mrampado/SnowballProject/InitialPrototype(Gen1)/BoardPhotos/IMG_3307.JPEG

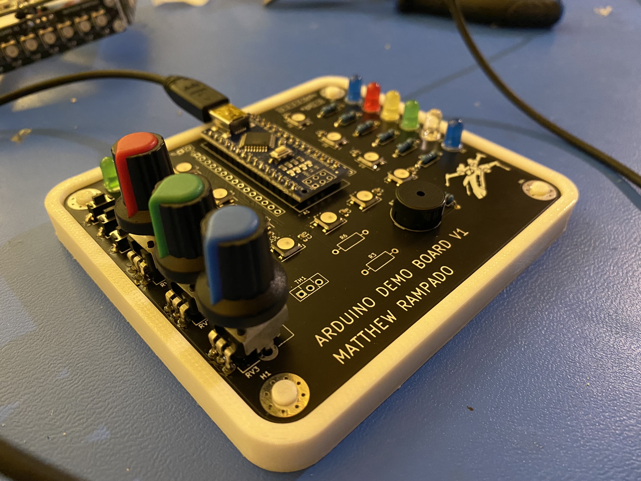
InitialPrototype(Gen1)/BoardPhotos/IMG_3307.JPEG
