mrampado/SnowballProject/InitialPrototype(Gen1)/BoardPhotos/IMG_3309.JPEG

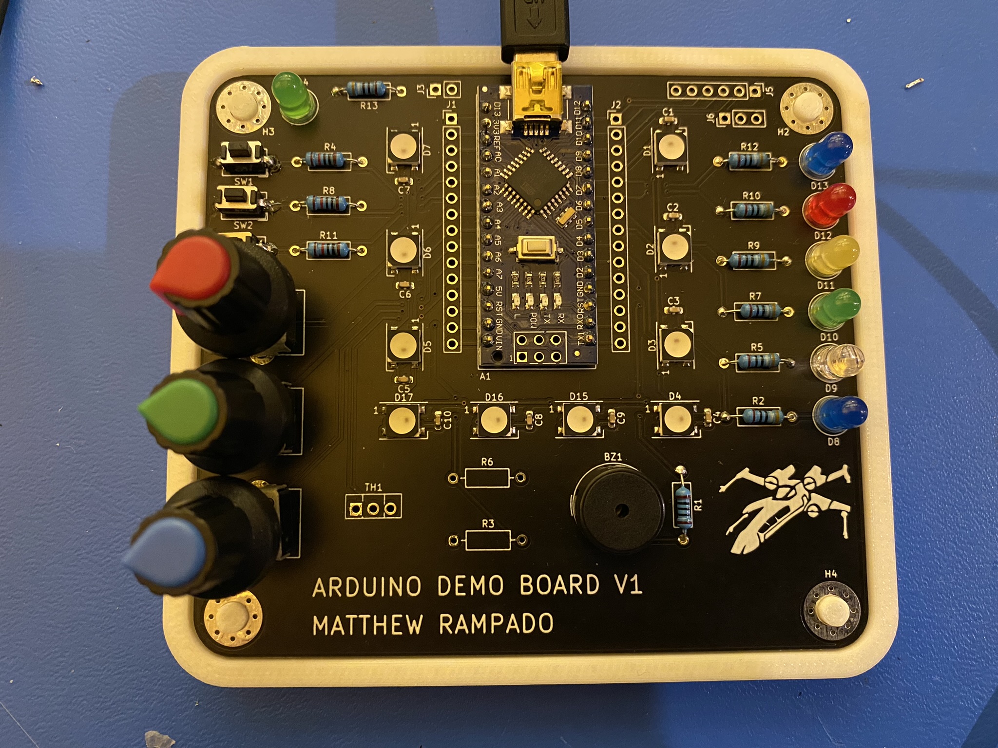
InitialPrototype(Gen1)/BoardPhotos/IMG_3309.JPEG
